giltesa/GBA-Wireless-Gamepad/4. SketchUP/GBA Wireless Gamepad B.jpg

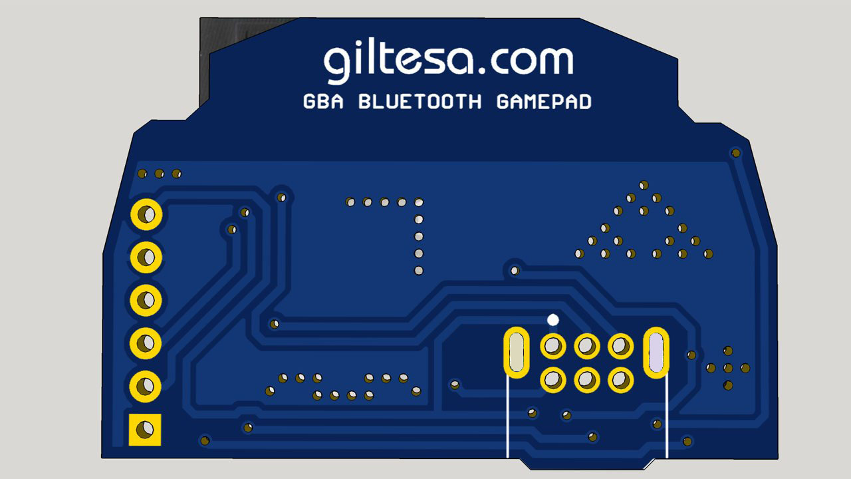
4. SketchUP/GBA Wireless Gamepad B.jpg
