giltesa/GBA-Wireless-Gamepad/4. SketchUP/GBA Wireless Gamepad T.jpg

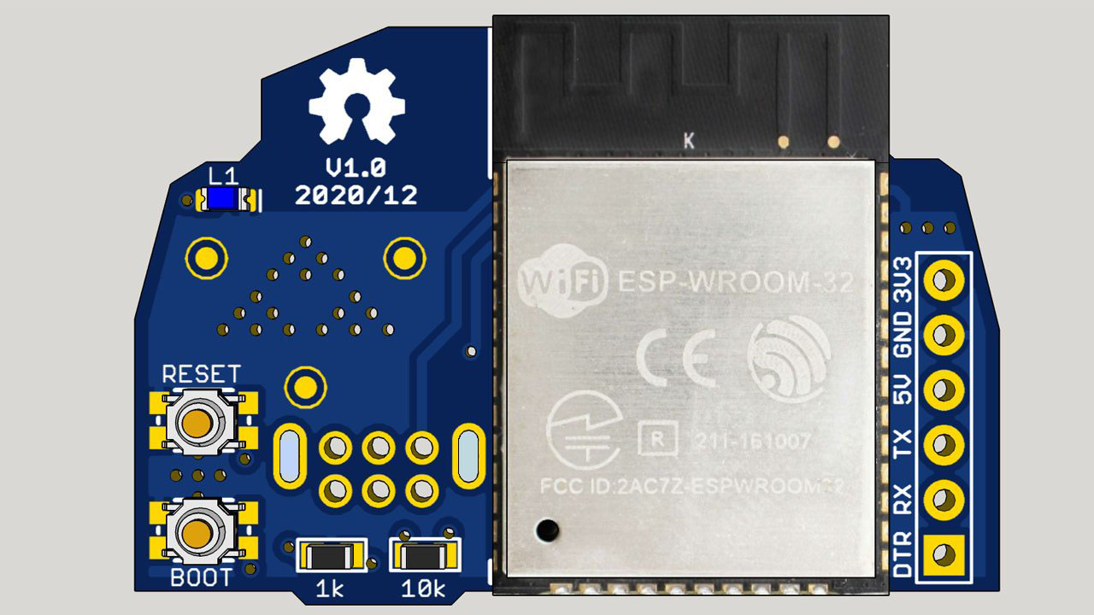
4. SketchUP/GBA Wireless Gamepad T.jpg
